nicolas5000/diagral-esp32/config/HardwareConfig.hpp

#pragma once

#include "driver/spi_master.h"
#include "esp_err.h"

namespace Config
{
    /// @brief Initialize hardware depending on config: NVS, LittleFS, GPIO ISR, SPI bus
    /// @return ESP_OK if no error
    esp_err_t InitHardware();

#ifdef CONFIG_CONNECTIVITY_CHOICE_ETH
    /// @brief Get SPI host used by W5500 Ethernet module from configuration
    /// @return SPI host
    spi_host_device_t GetEthernetSpiHost();
#endif
}
