nicolas5000/diagral-esp32/helpers/CmdLineManagement.cpp

#include "CmdLineManagement.hpp"
#include "MiscConfig.hpp"
#include "NetworkConfig.hpp"

#include <string.h>
#include "linenoise/linenoise.h"
#include "argtable3/argtable3.h"
#include "esp_console.h"
#include "esp_log.h"

using namespace Config;

static const char *TAG = "cmdline_mngt";
static Diagral::DiagralManager *sDiagralManager;
static esp_console_repl_t *sConsoleRepl;
static bool sLogin; // flag to synchronize login task

// ******************* REBOOT ********************

static int do_reboot_cmd(int argc, char **argv)
{
    esp_restart();
    return 0;
}

void register_reboot(void)
{
    const esp_console_cmd_t reboot_cmd = {
        .command = "reboot",
        .help = "Reboot ESP32",
        .hint = NULL,
        .func = &do_reboot_cmd,
        .argtable = NULL,
        .func_w_context = NULL,
        .context = NULL};

    ESP_ERROR_CHECK(esp_console_cmd_register(&reboot_cmd));
}

// ******************* LOGOUT ********************

static int do_logout_cmd(int argc, char **argv)
{
    sLogin = false;
    return 0;
}

void register_logout(void)
{
    const esp_console_cmd_t logout_cmd = {
        .command = "logout",
        .help = "Logout from ESP32 console",
        .hint = NULL,
        .func = &do_logout_cmd,
        .argtable = NULL,
        .func_w_context = NULL,
        .context = NULL};

    ESP_ERROR_CHECK(esp_console_cmd_register(&logout_cmd));
}

// ******************* PASSWORD CONFIG ********************

/// @brief Structure used by the 'config_password' command
static struct
{
    struct arg_lit *del;
    struct arg_str *password;
    struct arg_end *end;
} config_password_args;

static int do_config_password_cmd(int argc, char **argv)
{
    int nerrors = arg_parse(argc, argv, (void **)&config_password_args);
    if (nerrors != 0)
    {
        arg_print_errors(stderr, config_password_args.end, argv[0]);
        return 1;
    }
    if (config_password_args.del->count > 0)
    {
        MiscConfig::ResetAccessPassword();
        ESP_LOGI(TAG, "Password configuration restored to default values");
    }
    else
    {
        esp_err_t err;
        // Set configuration
        if (config_password_args.password->count > 0)
        {
            err = MiscConfig::SetAccessPassword(config_password_args.password->sval[0]);
            if (err != ESP_OK)
            {
                ESP_LOGE(TAG, "Failed to set password to configuration storage! (%d)", err);
            }
            else
            {
                ESP_LOGI(TAG, "Password set to configuration storage.");
            }
        }
    }
    return 0;
}

void register_config_password(void)
{
    config_password_args.del = arg_lit0("d", "delete", "Delete current configuration in storage (no other argument required)");
    config_password_args.password = arg_str0(NULL, "pass", "<password>", "Password (up to 32 characters)");
    config_password_args.end = arg_end(2);

    const esp_console_cmd_t config_password_cmd = {
        .command = "config_password",
        .help = "Configure console password (change is applied immediately)",
        .hint = NULL,
        .func = &do_config_password_cmd,
        .argtable = &config_password_args,
        .func_w_context = NULL,
        .context = NULL};

    ESP_ERROR_CHECK(esp_console_cmd_register(&config_password_cmd));
}

// ******************* Misc Register commands ********************

void register_misc_cmdline_tools()
{
    register_reboot();
    register_logout();
    register_config_password();
}

// ******************* LOGIN ********************

/// @brief Task to manage login
/// @param arg currently not used
static void cmd_line_task(void *arg)
{
    int32_t retry_counter = 0; // retry counter for failed attempts to login
    while (true)
    {
        bool login_success = false;
        if (MiscConfig::isAccessPasswordDefined())
        {
            // Read password
            linenoiseHistorySetMaxLen(0);
            char *input = linenoise("Enter password: ");
            if (input == NULL)
            {
                printf("Failed to read password\n");
            }
            else
            {
                std::string password(input);
                linenoiseFree(input);
                if (MiscConfig::CheckAccessPassword(password))
                {
                    printf("Login success!\n");
                    retry_counter = 0;
                    login_success = true;
                }
                else
                {
                    retry_counter++;
                    int32_t penalty = 2 * retry_counter;
                    printf("Login failed! %ld attempts failed, %ld seconds penalty!\n", retry_counter, penalty);
                    vTaskDelay(pdMS_TO_TICKS(penalty * 1000));
                }
            }
        }
        else
        {
            login_success = true;
        }
        if (login_success)
        {
            init_cmdline_tools();
            sLogin = true;
            while (sLogin) vTaskDelay(pdMS_TO_TICKS(1000)); // wait for logout
            vTaskDelay(pdMS_TO_TICKS(100));
            // Remove command line tools
            esp_console_stop_repl(sConsoleRepl);
            // Reinit console (deinit done by esp_console_stop_repl)
            init_console();
        }
    }
    return;
}

// ******************* INIT ********************

void init_console()
{
    // Initialize Command line tools
    sConsoleRepl = NULL;
    esp_console_repl_config_t repl_config = ESP_CONSOLE_REPL_CONFIG_DEFAULT();
    repl_config.prompt = "diagral-uart-esp32>";

    // install console REPL environment
#if CONFIG_ESP_CONSOLE_UART
    esp_console_dev_uart_config_t uart_config = ESP_CONSOLE_DEV_UART_CONFIG_DEFAULT();
    ESP_ERROR_CHECK(esp_console_new_repl_uart(&uart_config, &repl_config, &sConsoleRepl));
#elif CONFIG_ESP_CONSOLE_USB_CDC
    esp_console_dev_usb_cdc_config_t cdc_config = ESP_CONSOLE_DEV_CDC_CONFIG_DEFAULT();
    ESP_ERROR_CHECK(esp_console_new_repl_usb_cdc(&cdc_config, &repl_config, &sConsoleRepl));
#elif CONFIG_ESP_CONSOLE_USB_SERIAL_JTAG
    esp_console_dev_usb_serial_jtag_config_t usbjtag_config = ESP_CONSOLE_DEV_USB_SERIAL_JTAG_CONFIG_DEFAULT();
    ESP_ERROR_CHECK(esp_console_new_repl_usb_serial_jtag(&usbjtag_config, &repl_config, &sConsoleRepl));
#endif
}

void init_cmdline(Diagral::DiagralManager *diagral_manager)
{
    sDiagralManager = diagral_manager;
    sConsoleRepl = NULL;
    init_console();
    // launch login task
    xTaskCreate(cmd_line_task, "process_log_task", 4096, NULL, tskIDLE_PRIORITY, NULL);
}

void init_cmdline_tools()
{
    register_diagral_cmdline_tools(sDiagralManager);
    register_misc_cmdline_tools();
    register_network_config_cmdline_tools();
    register_mqtt_config_cmdline_tools();
    register_syslog_config_cmdline_tools();

    printf("\n ==============================================================\n");
    printf(" |            Steps to Use diagral-uart-esp3                  |\n");
    printf(" |                                                            |\n");
    printf(" |  Try 'help' to check all supported commands                |\n");
    printf(" |  Try TAB for commands auto-completion                      |\n");
    printf(" |                                                            |\n");
    printf(" ==============================================================\n\n");

    // start console REPL
    ESP_ERROR_CHECK(esp_console_start_repl(sConsoleRepl));
}
